mgaitan/cads/outputs/screenshots/AA/bottom.png

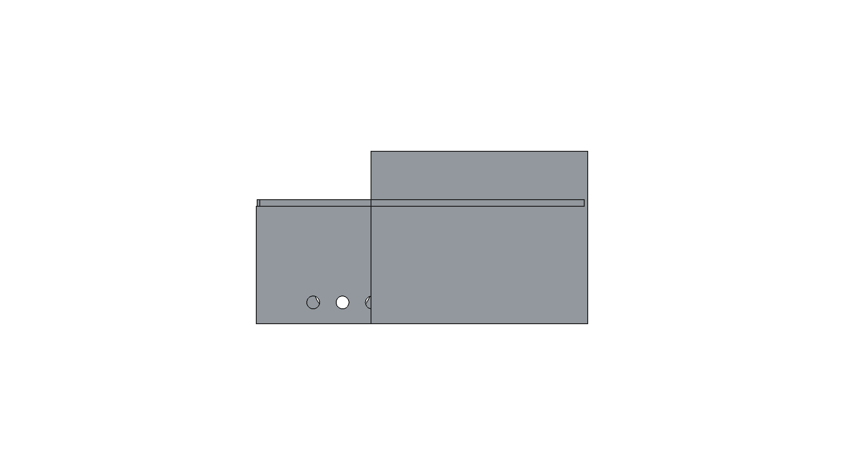
outputs/screenshots/AA/bottom.png
