mgaitan/cads/outputs/screenshots/AA/front.png

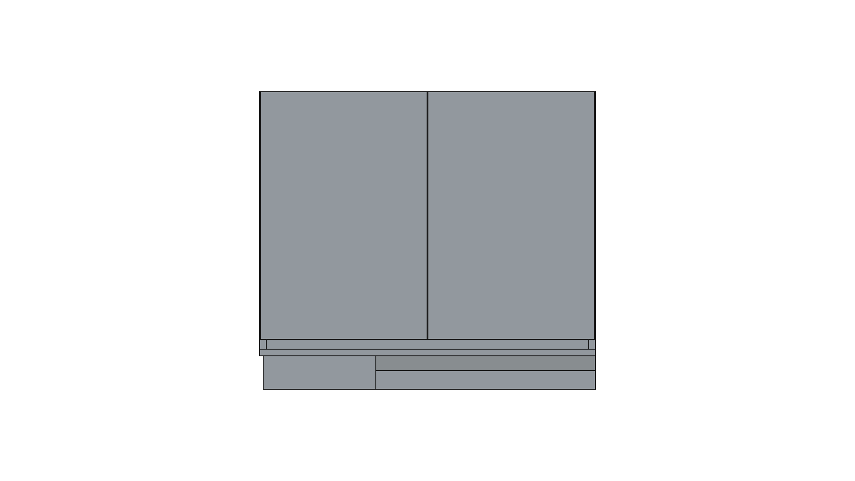
outputs/screenshots/AA/front.png
