mgaitan/cads/outputs/screenshots/AA/iso.png

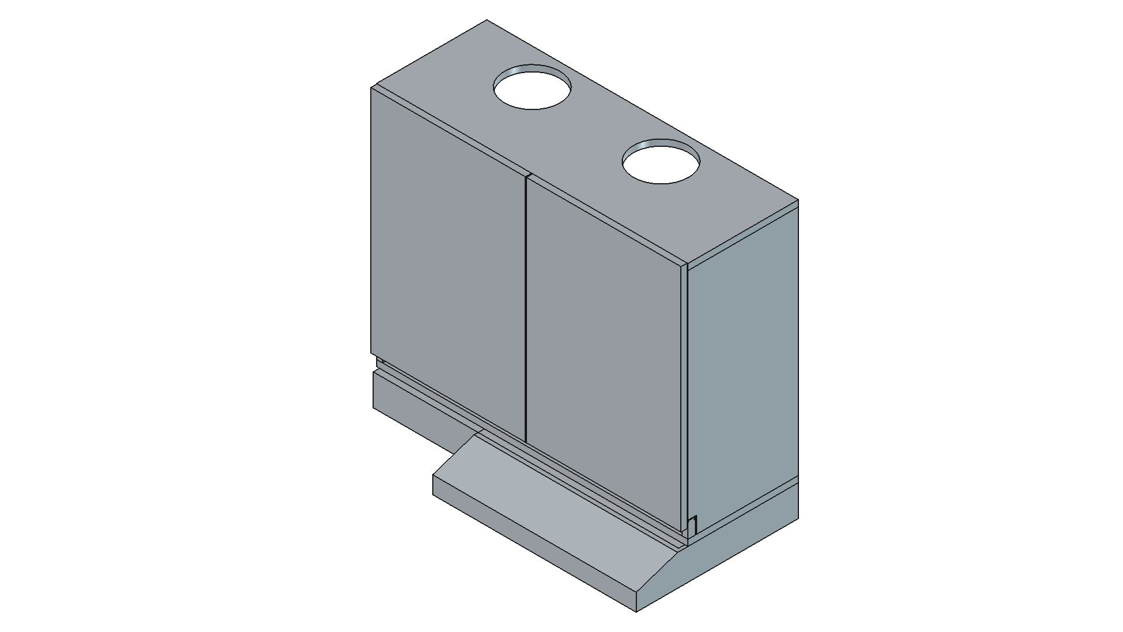
outputs/screenshots/AA/iso.png
