mgaitan/cads/outputs/screenshots/AA/left.png

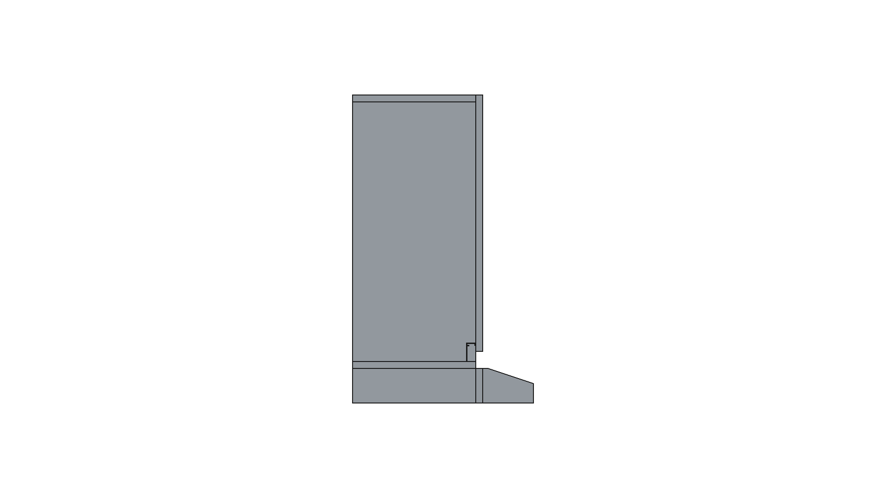
outputs/screenshots/AA/left.png
