mgaitan/cads/outputs/screenshots/AA/right.png

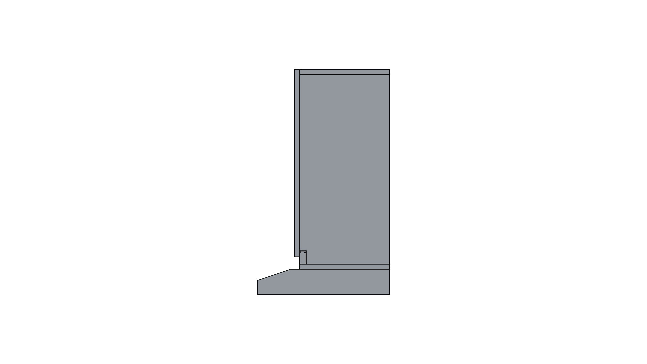
outputs/screenshots/AA/right.png
