mgaitan/cads/outputs/screenshots/AB/bottom.png

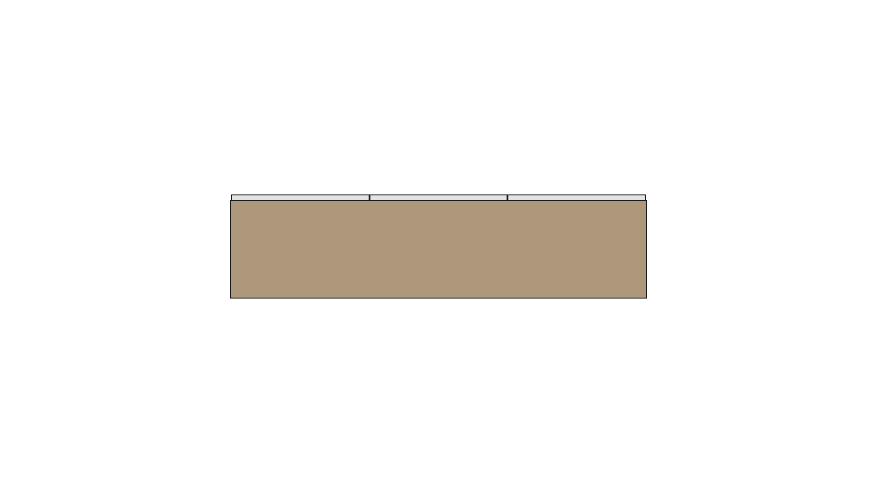
outputs/screenshots/AB/bottom.png
