mgaitan/cads/outputs/screenshots/AB/iso.png

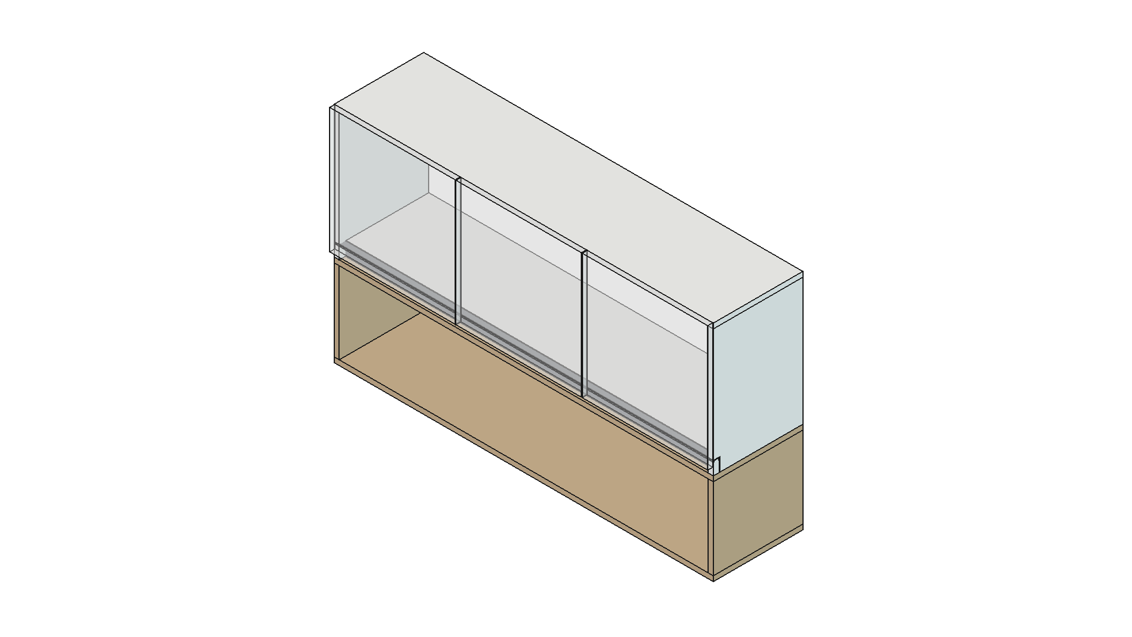
outputs/screenshots/AB/iso.png
