mgaitan/cads/outputs/screenshots/AB/left.png

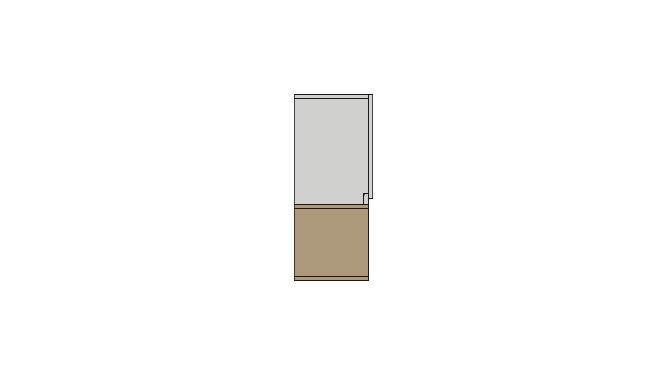
outputs/screenshots/AB/left.png
