mgaitan/cads/outputs/screenshots/BA/front.png

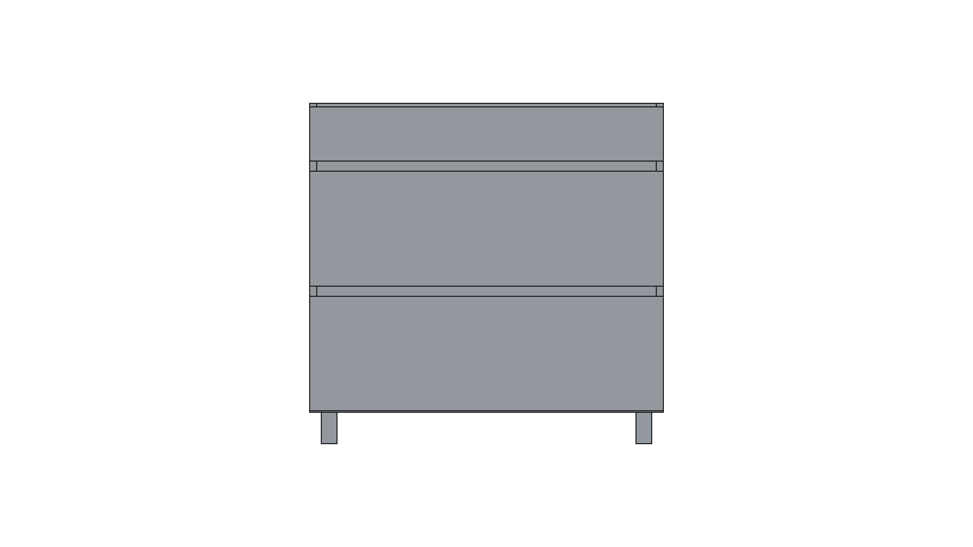
outputs/screenshots/BA/front.png
