mgaitan/cads/outputs/screenshots/BA/iso.png

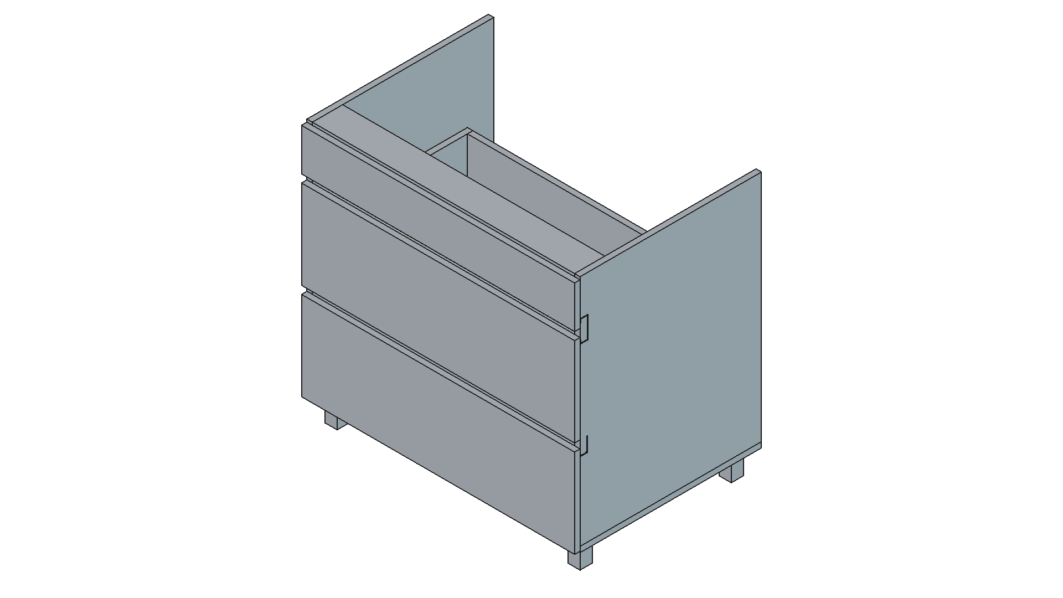
outputs/screenshots/BA/iso.png
