mgaitan/cads/outputs/screenshots/BB/top.png

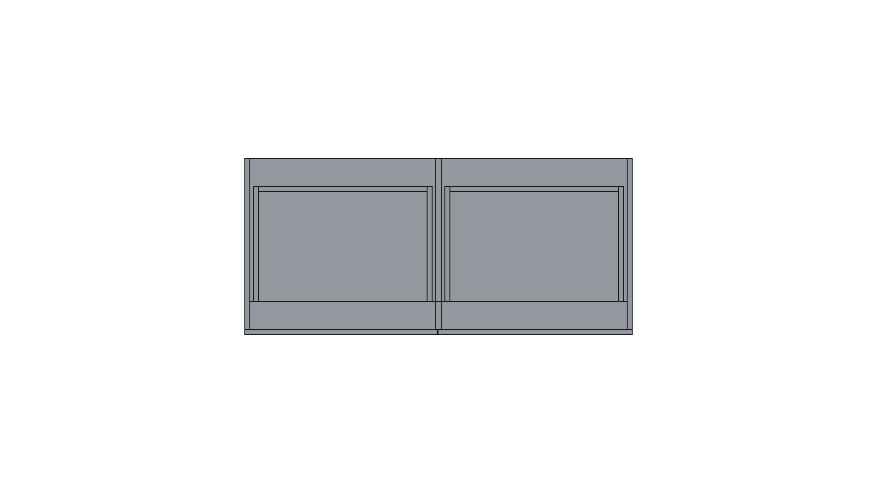
outputs/screenshots/BB/top.png
