mgaitan/cads/outputs/screenshots/ENS/bottom.png

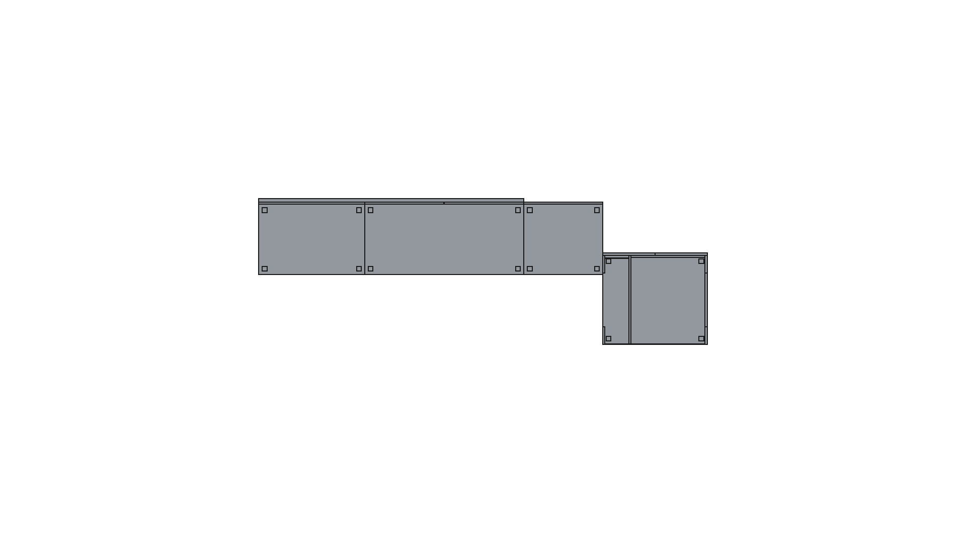
outputs/screenshots/ENS/bottom.png
