mgaitan/cads/outputs/screenshots/ENS/iso.png

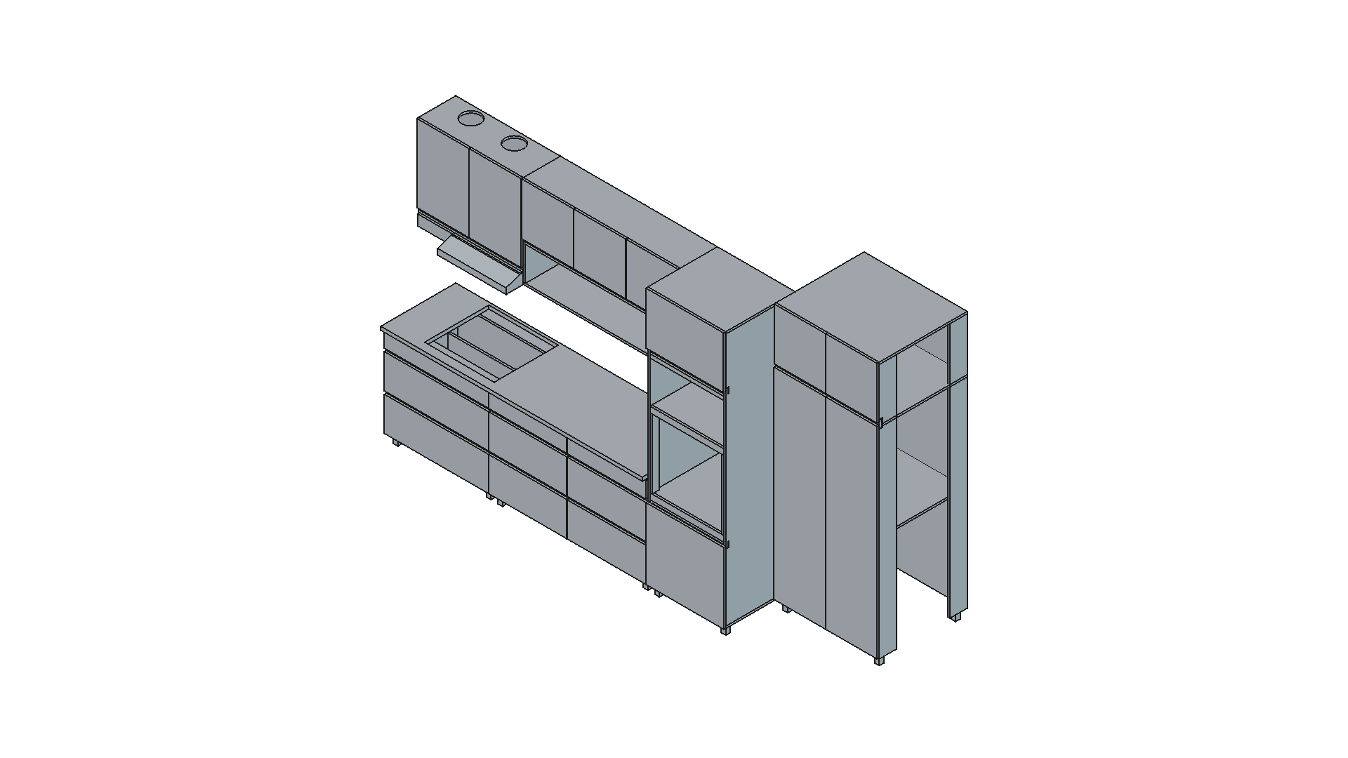
outputs/screenshots/ENS/iso.png
