mgaitan/cads/outputs/screenshots/ENS/top.png

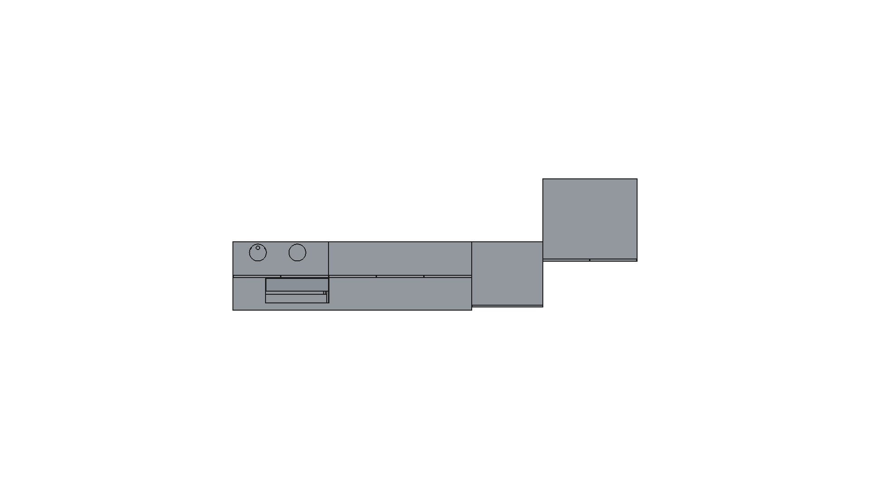
outputs/screenshots/ENS/top.png
