mgaitan/cads/outputs/screenshots/ENSI/front.png

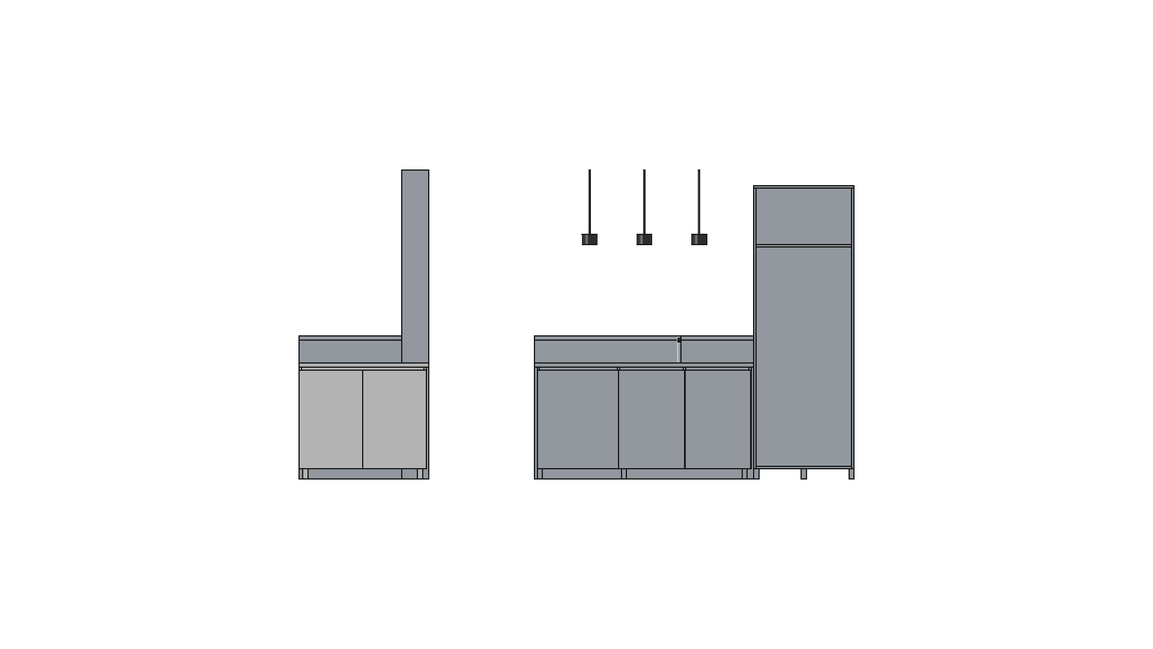
outputs/screenshots/ENSI/front.png
