mgaitan/cads/outputs/screenshots/ENSI/iso.png

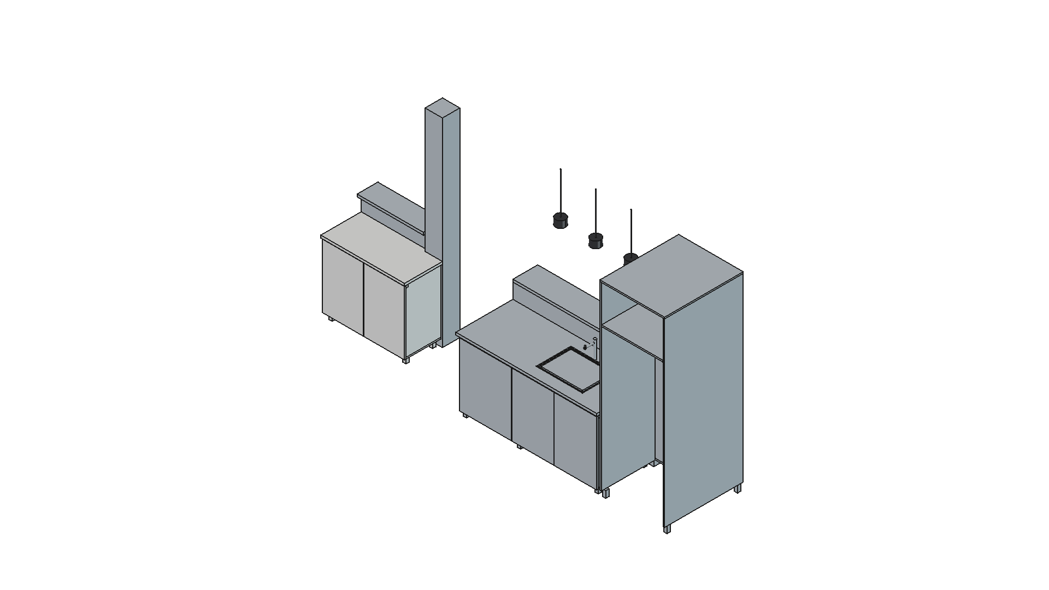
outputs/screenshots/ENSI/iso.png
