mgaitan/cads/outputs/screenshots/ENSI/rear.png

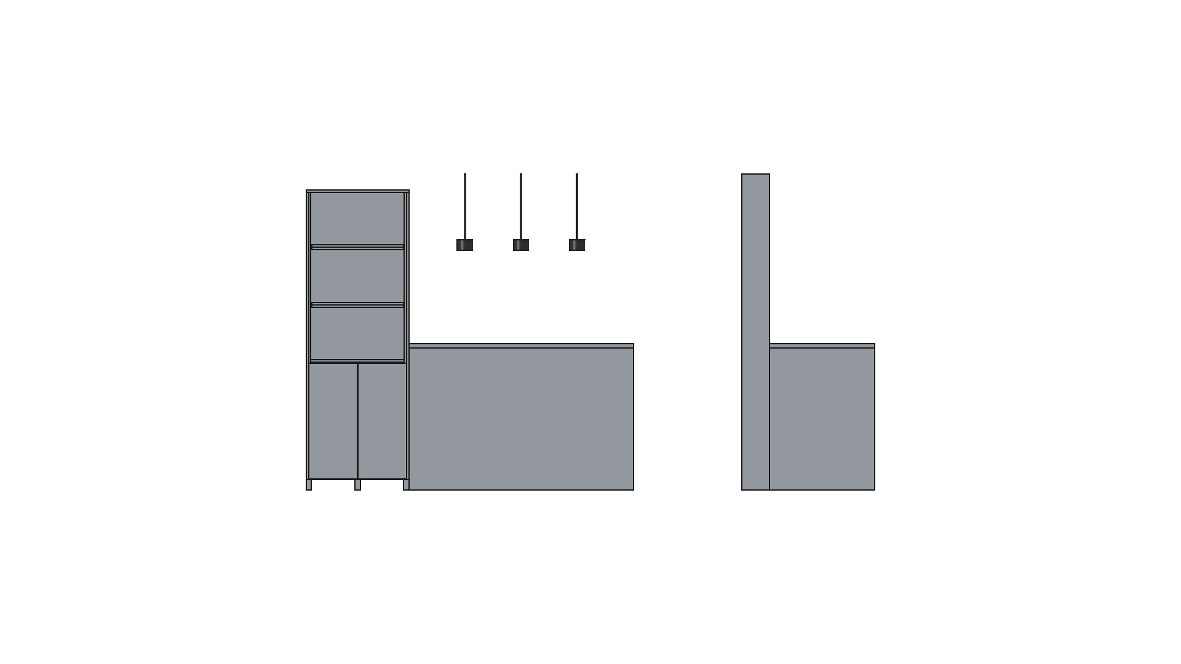
outputs/screenshots/ENSI/rear.png
