mgaitan/cads/outputs/screenshots/F/front.png

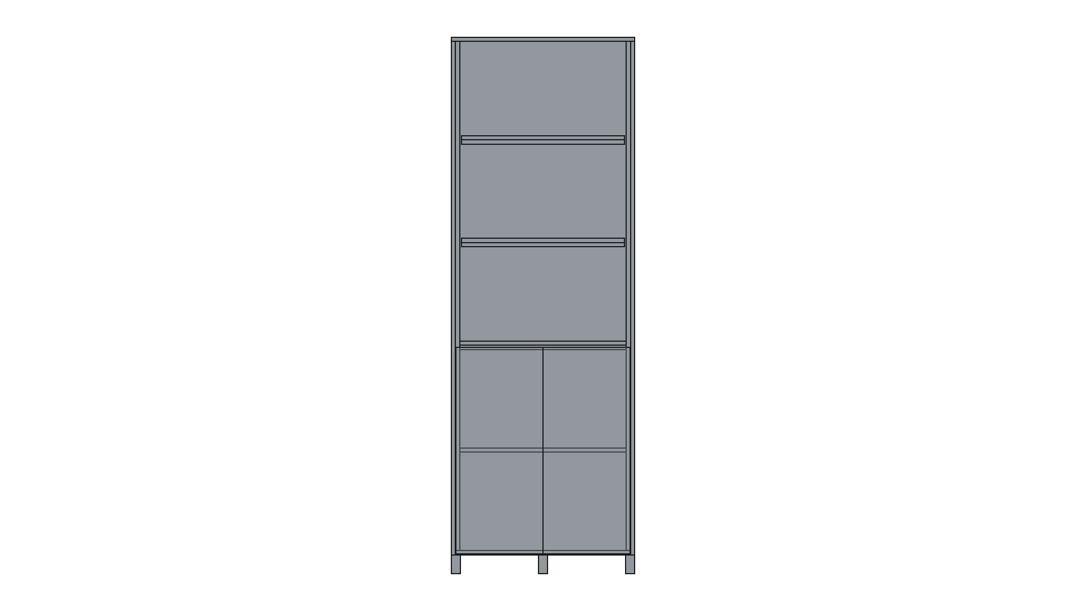
outputs/screenshots/F/front.png
