mgaitan/cads/outputs/screenshots/FULL/bottom.png

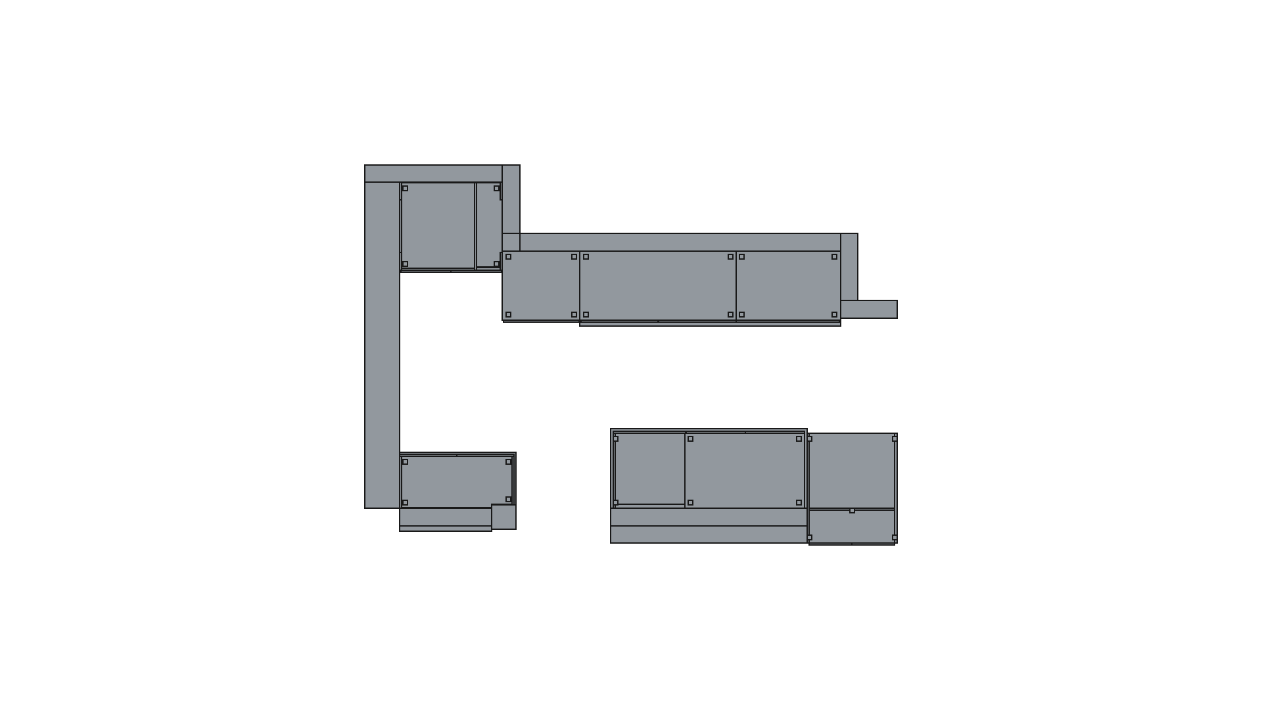
outputs/screenshots/FULL/bottom.png
