mgaitan/cads/outputs/screenshots/FULL/iso.png

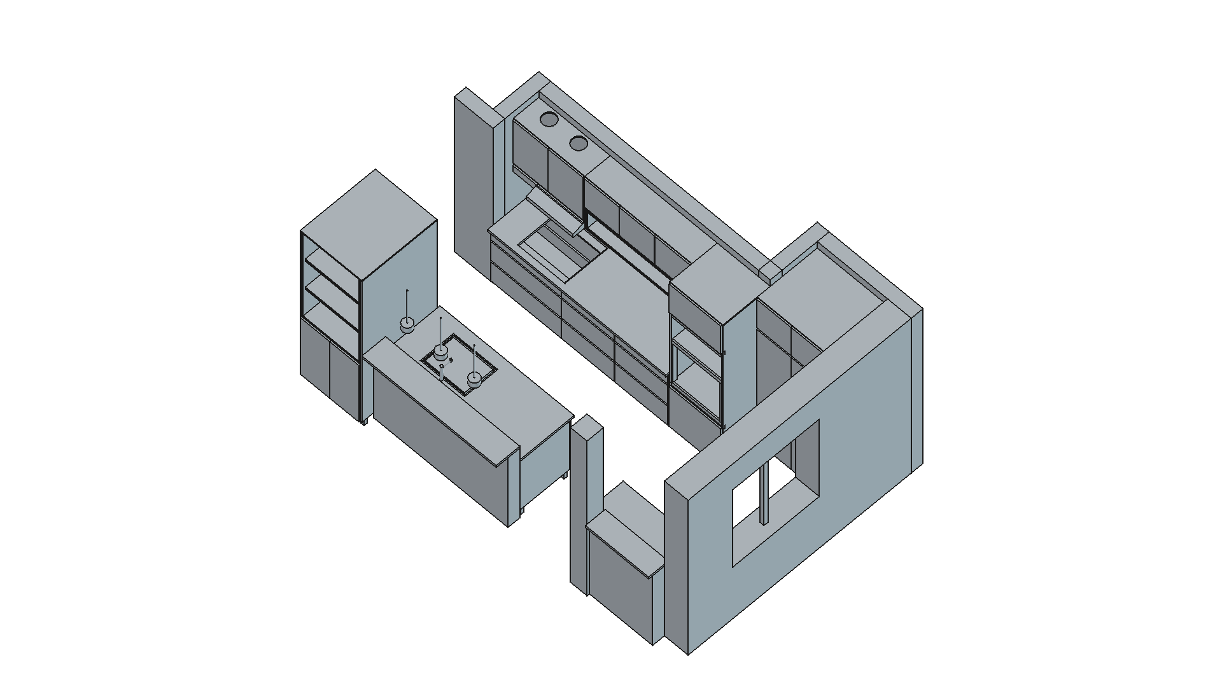
outputs/screenshots/FULL/iso.png
