mgaitan/cads/outputs/screenshots/FULL/left.png

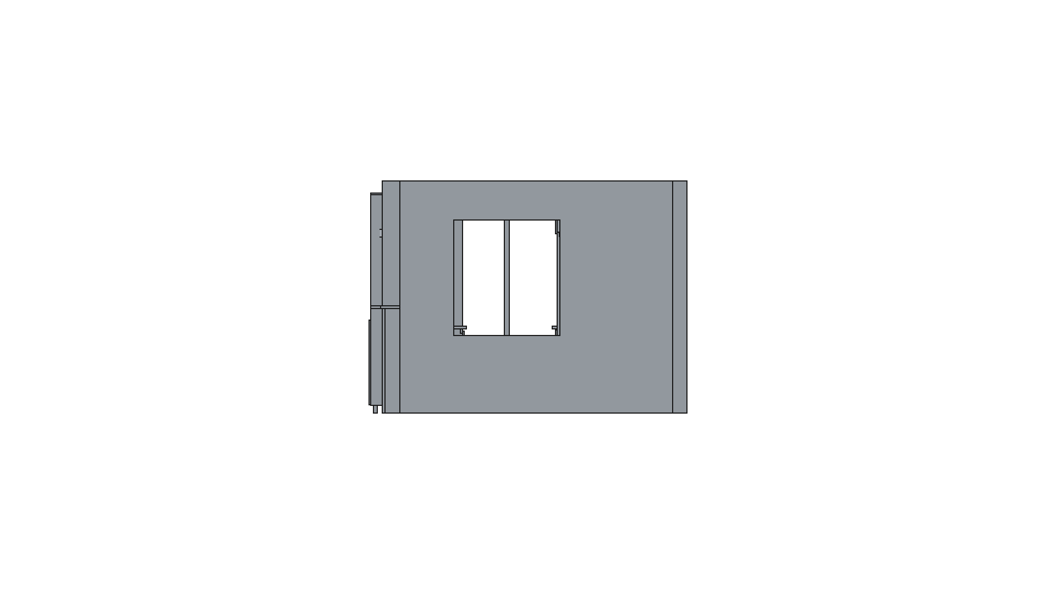
outputs/screenshots/FULL/left.png
