mgaitan/cads/outputs/screenshots/FULL/top.png

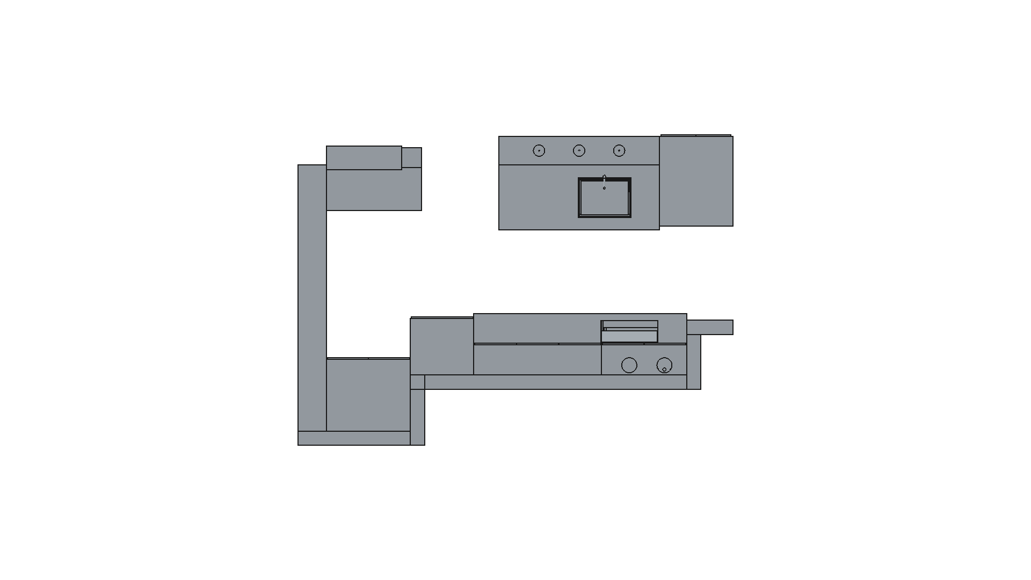
outputs/screenshots/FULL/top.png
