mgaitan/cads/outputs/screenshots/H/front.png

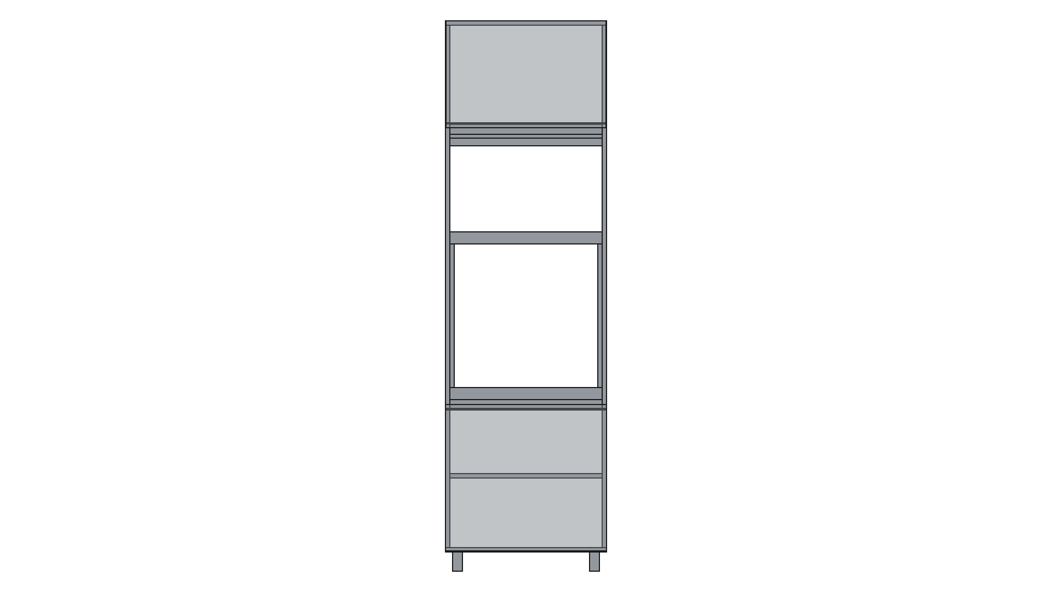
outputs/screenshots/H/front.png
