mgaitan/cads/outputs/screenshots/I/front.png

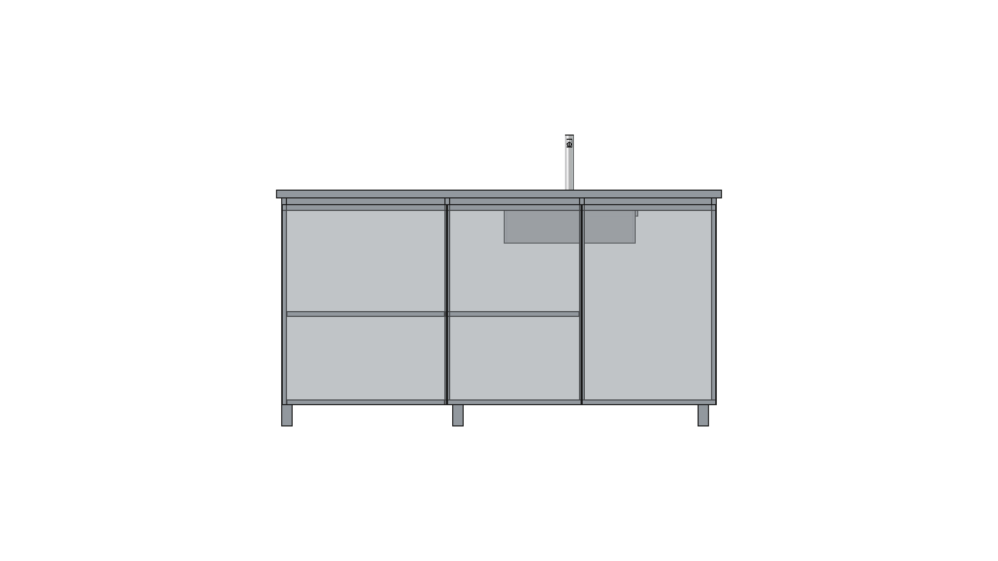
outputs/screenshots/I/front.png
