mgaitan/cads/outputs/screenshots/I/rear.png

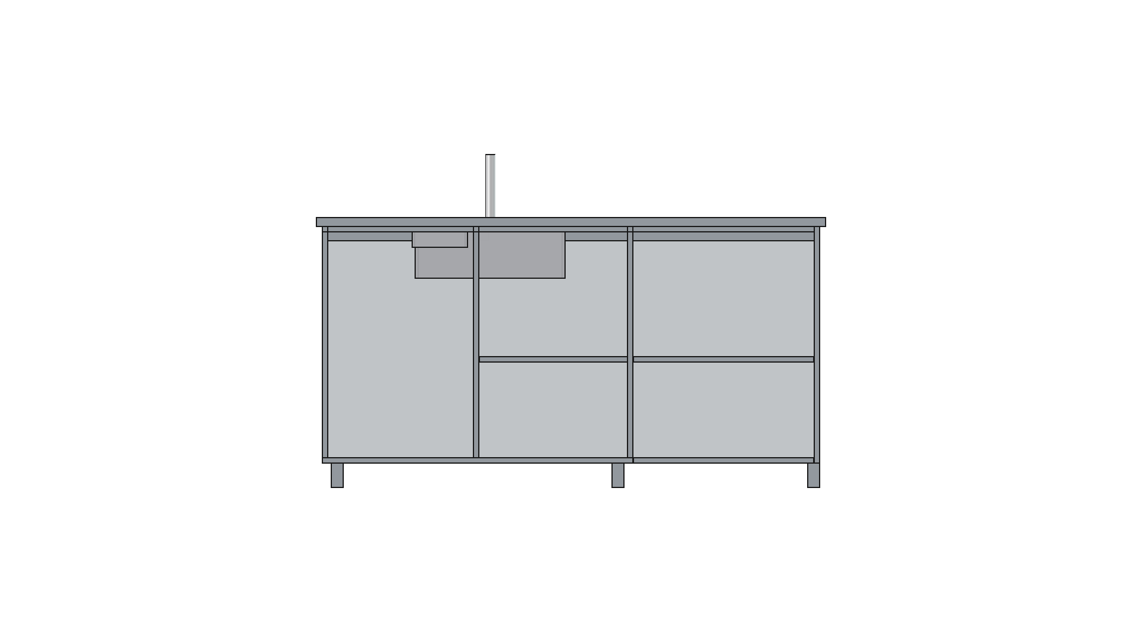
outputs/screenshots/I/rear.png
