mgaitan/cads/outputs/screenshots/M/bottom.png

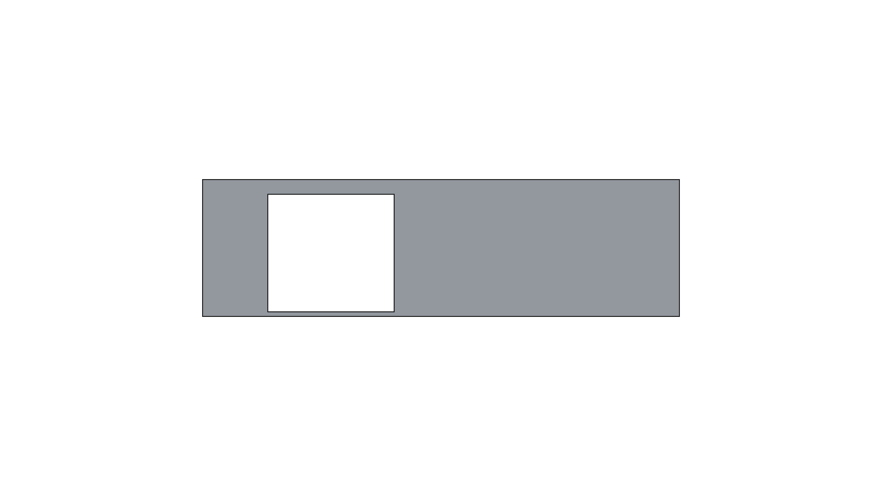
outputs/screenshots/M/bottom.png
