mgaitan/cads/outputs/screenshots/M/iso.png

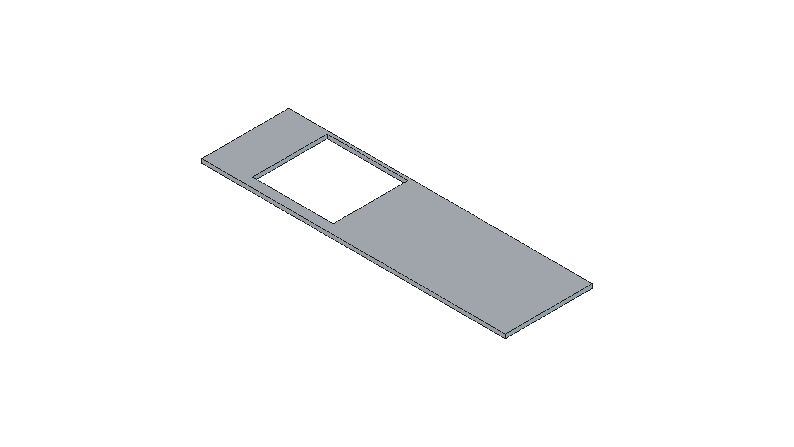
outputs/screenshots/M/iso.png
