mgaitan/cads/outputs/screenshots/R/rear.png

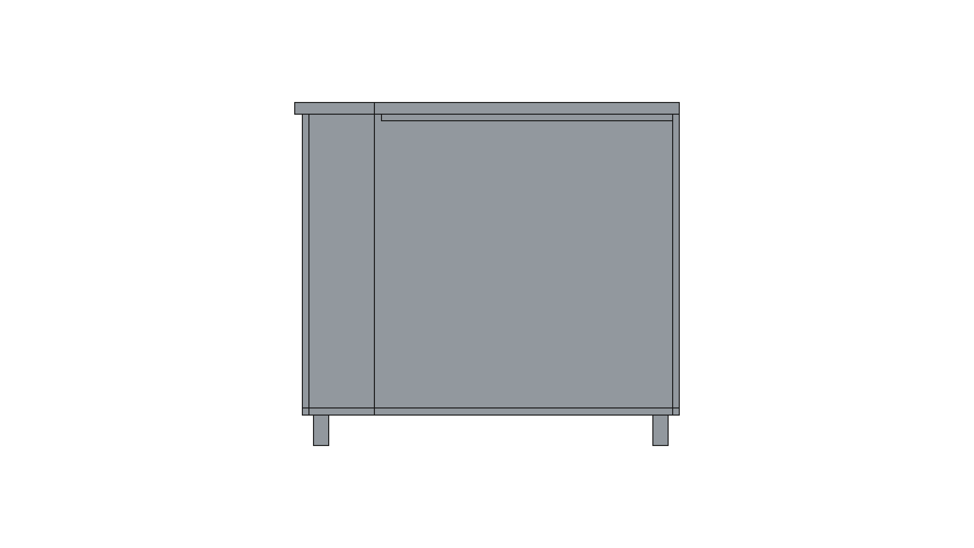
outputs/screenshots/R/rear.png
