mgaitan/cads/outputs/site/assets/models/AB.stl

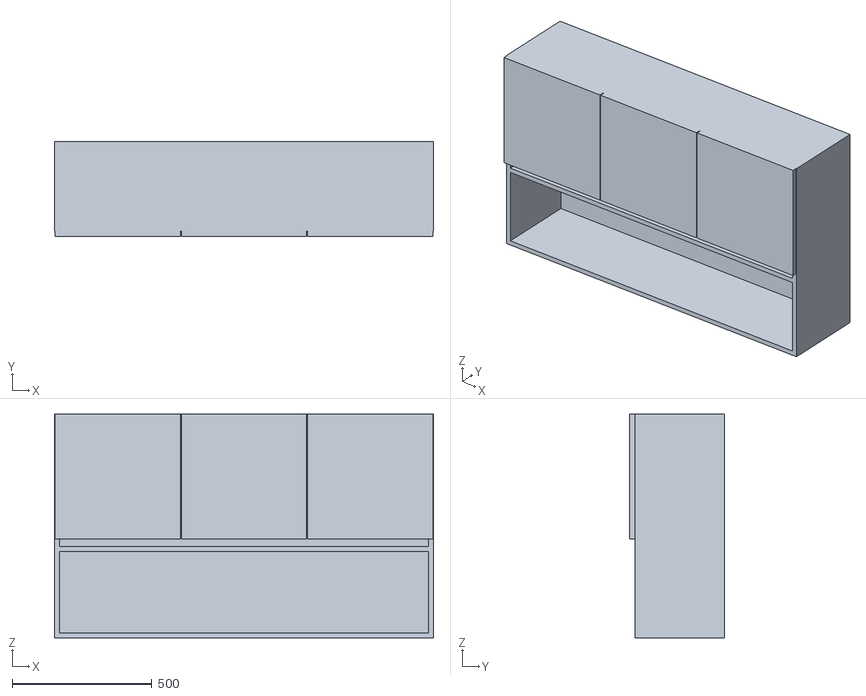
[picture p45: CAD file, 2026-03-17]
outputs/site/assets/models/AB.stl
1355.0 x 338.0 x 800.0
