mgaitan/cads/models/ENS.FCStd

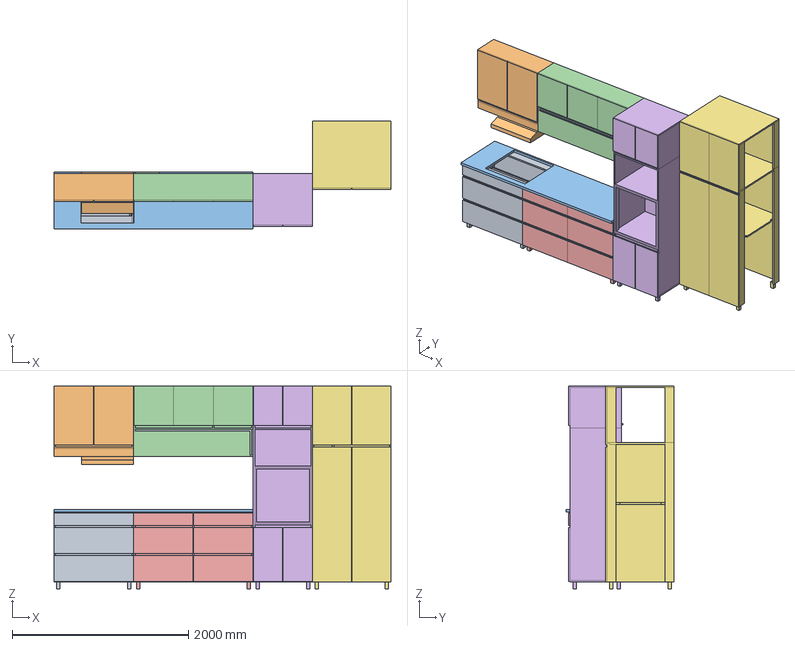
[picture p46: CAD file, 2026-03-25]
models/ENS.FCStd
3820.0 x 1225.0 x 2300.0 mm
BA_Bajo_Izq
AA_Alacena_Izq
M_Mesada
ABAC_Alacena_Der
BB_Bajo_Der
H_Columna
L_Armario_Lavadero
