mgaitan/cads/outputs/site/assets/models/BA.stl

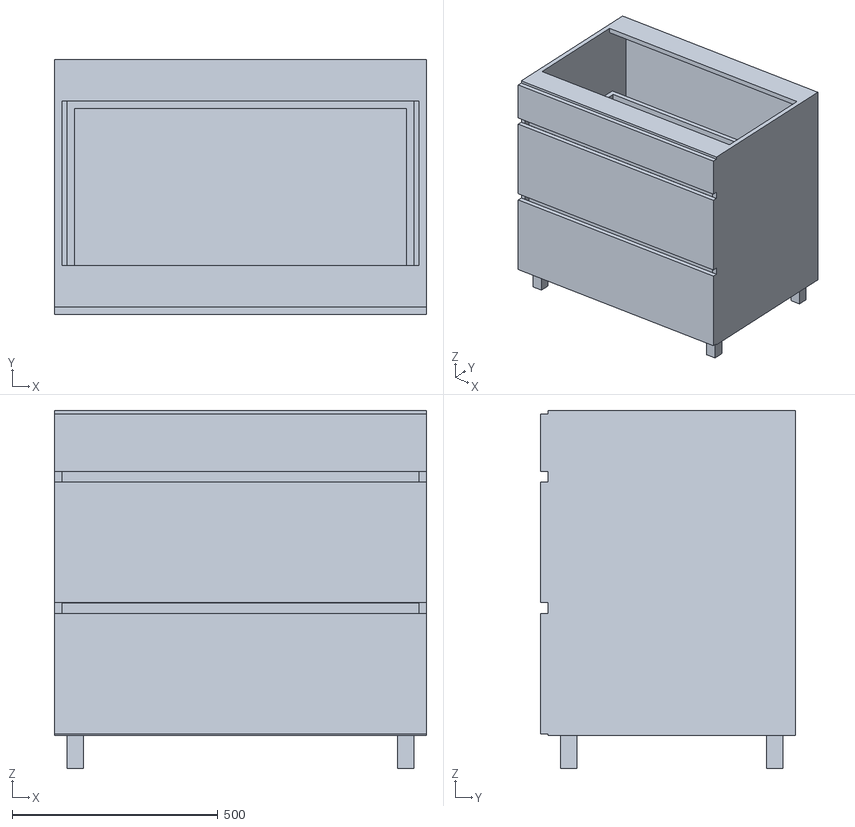
[picture p47: CAD file, 2026-03-17]
outputs/site/assets/models/BA.stl
903.0 x 618.0 x 870.0
