mgaitan/cads/models/AA.FCStd

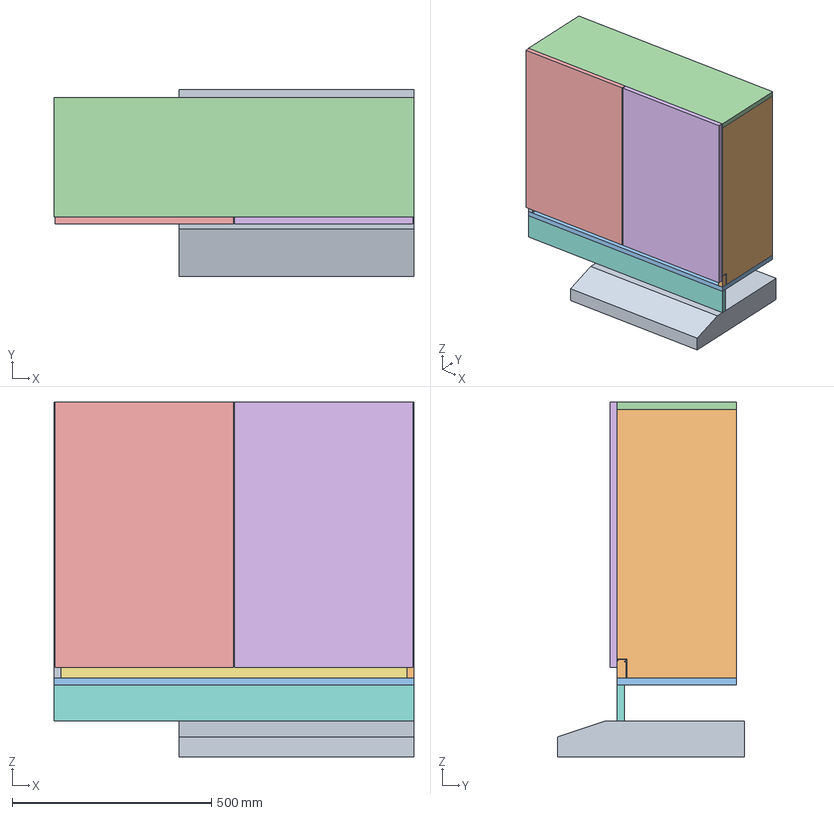
[picture p48: CAD file, 2026-03-25]
models/AA.FCStd
903.0 x 470.0 x 890.0 mm
AA1_Lateral_Izq
AA2_Lateral_Der
AA3_Piso_Casco
AA4_Tapa_Casco
AA8_Frente_Izq
AA9_Frente_Der
AA12_Gola_J_Inferior
AA10_Liston_Fijo_90
AA11_Extractor_Ref
