mgaitan/cads/outputs/site/assets/models/AA.stl

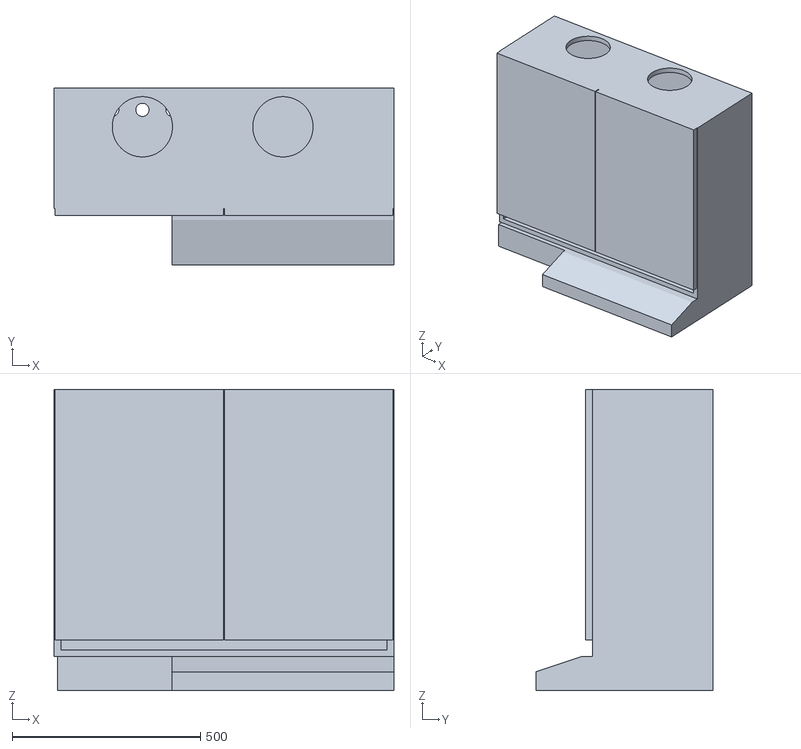
[picture p49: CAD file, 2026-03-17]
outputs/site/assets/models/AA.stl
903.0 x 470.0 x 800.0
