mgaitan/cads/models/H.FCStd

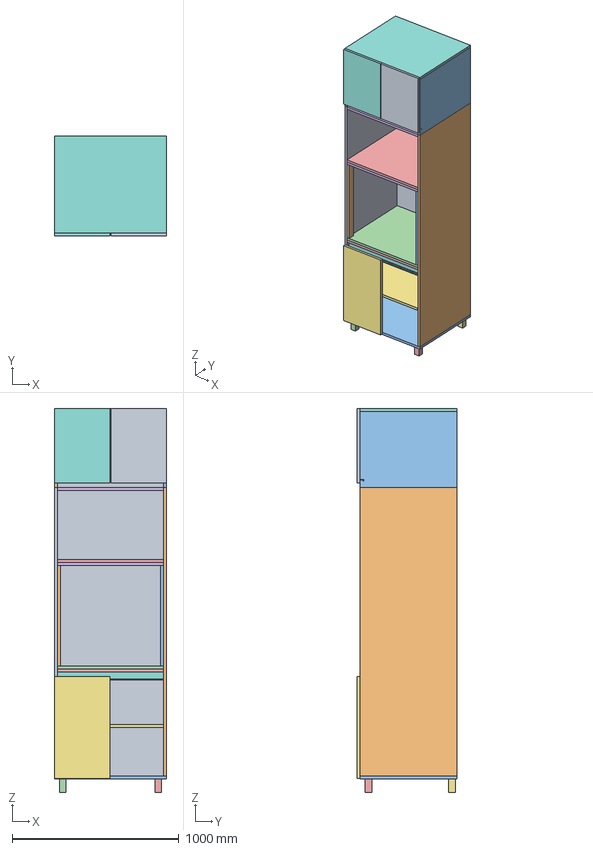
[picture p50: CAD file, 2026-03-19]
models/H.FCStd
672.0 x 598.0 x 2300.0 mm
H1_Lateral_Izq
H2_Lateral_Der
H3_Piso_Casco
H3L_Pata_1
H3L_Pata_2
H3L_Pata_3
H3L_Pata_4
H4_Tapa_Casco
H14_Fondo_3mm
H15_Liston_Vert_Izq
H16_Liston_Vert_Der
H5_Piso_Horno
H6_Piso_Micro
H7_Tapa_Micro
H8_Estante_Inferior
H17_Gola_J_Continuidad
H18_Gola_J_Sup
H1B_Lateral_Izq_Sup
H2B_Lateral_Der_Sup
H19_Piso_Alacena_Sup
H12B_Regrueso_Horizontal_Inferior_50
H9B_Regrueso_Horizontal_Sup_50
H10A_Puerta_Inferior_Izq
H11A_Puerta_Superior_Izq
H11B_Puerta_Superior_Der
