mgaitan/cads/outputs/site/assets/models/F.stl

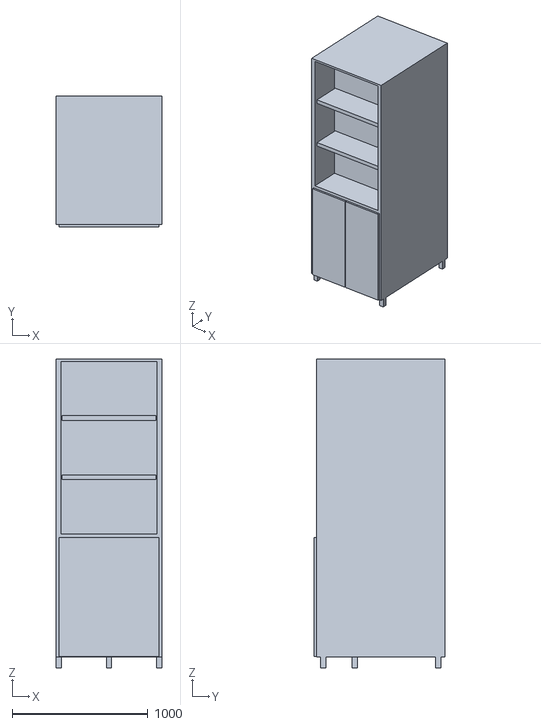
[picture p51: CAD file, 2026-03-17]
outputs/site/assets/models/F.stl
780.0 x 968.0 x 2278.0
