mgaitan/cads/models/BB.FCStd

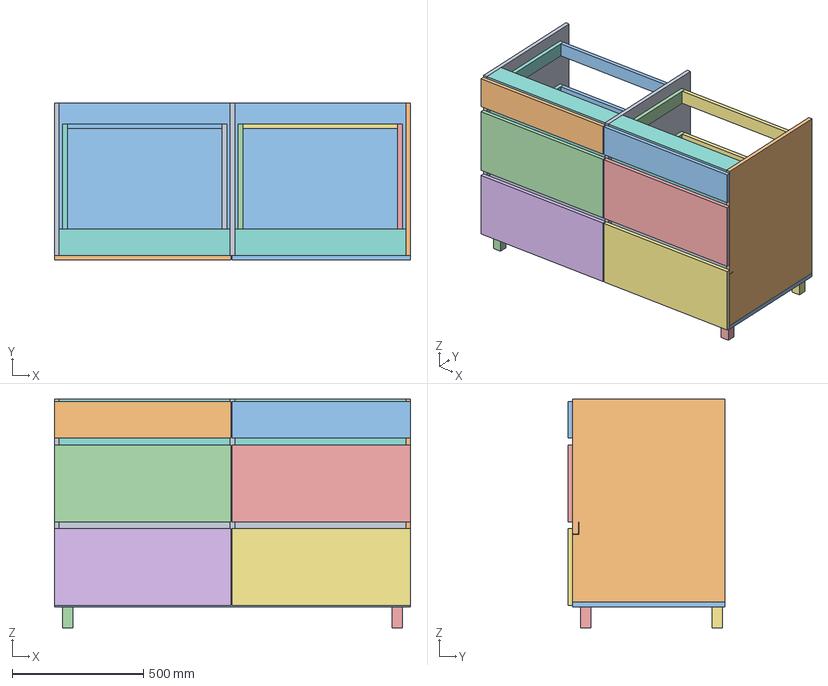
[picture p52: CAD file, 2026-03-19]
models/BB.FCStd
1355.0 x 598.0 x 870.0 mm
BB1_Lateral_Izq
BB2_Lateral_Der
BB3_Piso_Pasante
BB3L_Pata_1
BB3L_Pata_2
BB3L_Pata_3
BB3L_Pata_4
BB5_Soporte_Superior_Frente
BB7_Divisor_Central
BB8_Frente_Top_Izq
BB9_Frente_Top_Der
BB10_Frente_Mid_Izq
BB11_Frente_Mid_Der
BB12_Frente_Bot_Izq
BB13_Frente_Bot_Der
BB14_Caja_Top_Izq_Lateral_Izq
BB14_Caja_Top_Izq_Lateral_Der
BB14_Caja_Top_Izq_Frente_Caja
BB14_Caja_Top_Izq_Trasera_Caja
BB15_Caja_Top_Der_Lateral_Izq
BB15_Caja_Top_Der_Lateral_Der
BB15_Caja_Top_Der_Frente_Caja
BB15_Caja_Top_Der_Trasera_Caja
BB16_Caja_Mid_Izq_Lateral_Izq
BB16_Caja_Mid_Izq_Lateral_Der
BB16_Caja_Mid_Izq_Frente_Caja
BB16_Caja_Mid_Izq_Trasera_Caja
BB17_Caja_Mid_Der_Lateral_Izq
BB17_Caja_Mid_Der_Lateral_Der
BB17_Caja_Mid_Der_Frente_Caja
BB17_Caja_Mid_Der_Trasera_Caja
BB18_Caja_Bot_Izq_Lateral_Izq
BB18_Caja_Bot_Izq_Lateral_Der
BB18_Caja_Bot_Izq_Frente_Caja
BB18_Caja_Bot_Izq_Trasera_Caja
BB19_Caja_Bot_Der_Lateral_Izq
BB19_Caja_Bot_Der_Lateral_Der
BB19_Caja_Bot_Der_Frente_Caja
BB19_Caja_Bot_Der_Trasera_Caja
BB20_Gola_C_Superior
BB21_Gola_J_Media
