mgaitan/cads/outputs/site/assets/models/R.stl

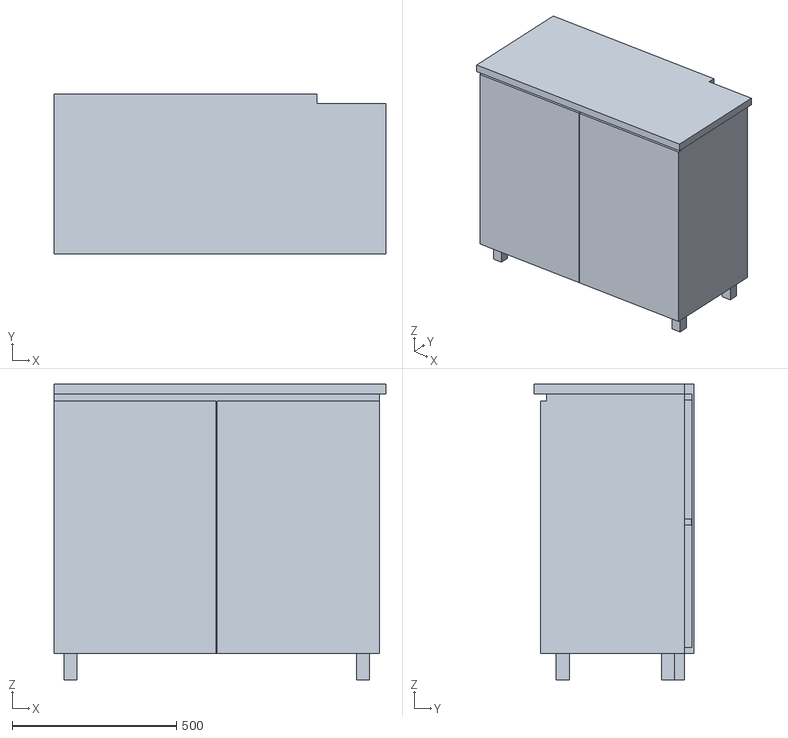
[picture p53: CAD file, 2026-03-17]
outputs/site/assets/models/R.stl
1010.0 x 488.0 x 900.0
