mgaitan/cads/models/AB.FCStd

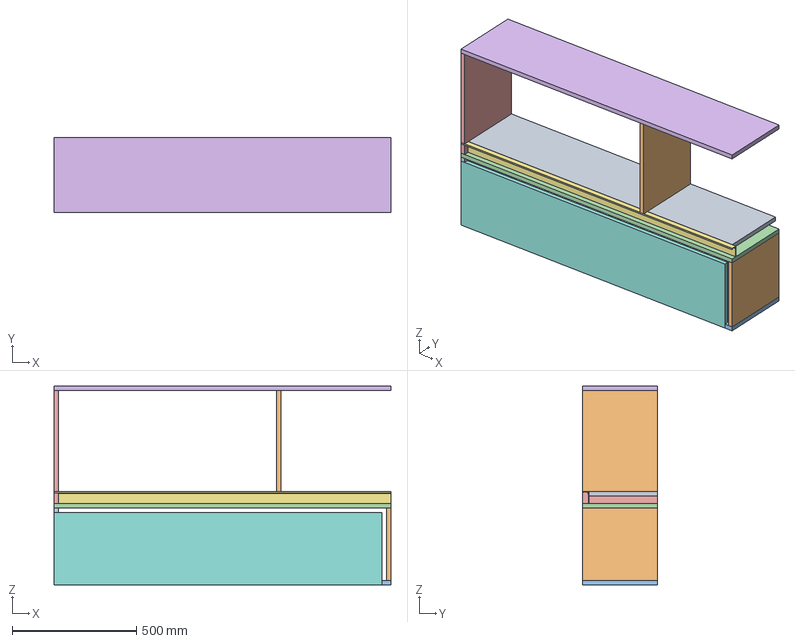
[picture p54: CAD file, 2026-03-19]
models/AB.FCStd
1355.0 x 300.0 x 800.0 mm
AC1_Lateral_Izq
AC2_Lateral_Der
AC3_Piso
AC4_Tapa
AB1_Lateral_Izq
AB4_Tapa
AB9_Gola_J_Inferior
AC5_Fondo_18mm
AB3_Piso
AB10_Divisor_Der_Puerta_Central
