mgaitan/cads/outputs/site/assets/models/BB.stl

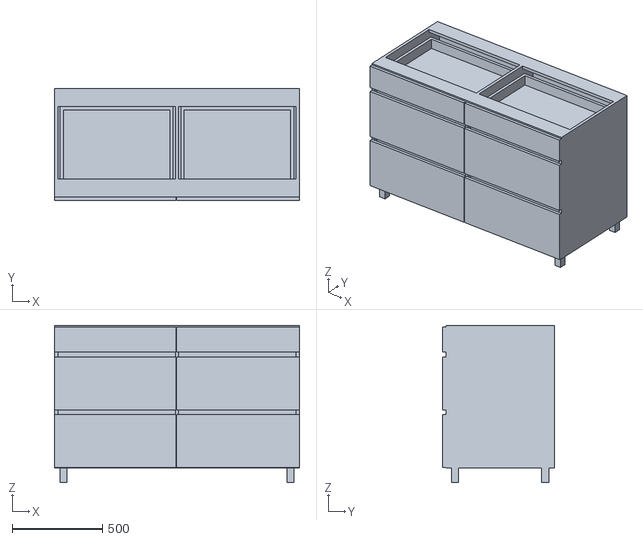
[picture p55: CAD file, 2026-03-17]
outputs/site/assets/models/BB.stl
1355.0 x 618.0 x 870.0
