mgaitan/cads/models/BA.FCStd

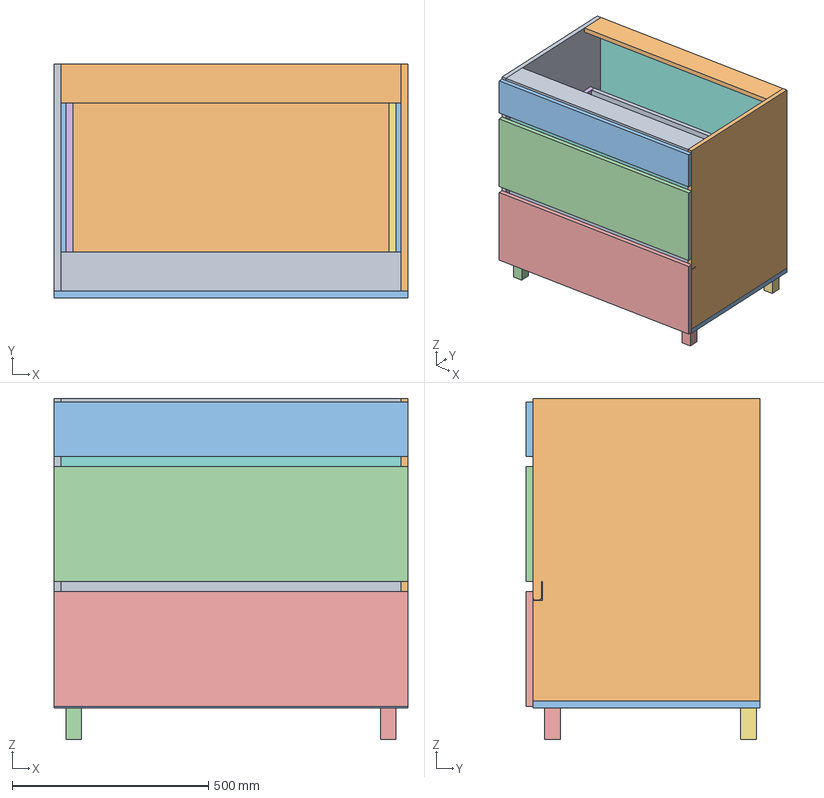
[picture p56: CAD file, 2026-03-19]
models/BA.FCStd
903.0 x 598.0 x 870.0 mm
BA1_Lateral_Izq
BA2_Lateral_Der
BA3_Piso_Pasante
BA3L_Pata_1
BA3L_Pata_2
BA3L_Pata_3
BA3L_Pata_4
BA4_Fondo_3mm
BA5_Soporte_Superior_Frente
BA6_Soporte_Superior_Fondo
BA9_Frente_Falso_Sup
BA10_Frente_Mid
BA11_Frente_Bot
BA14_Caja_Mid_Lateral_Izq
BA14_Caja_Mid_Lateral_Der
BA14_Caja_Mid_Frente_Caja
BA14_Caja_Mid_Trasera_Caja
BA14_Caja_Mid_Fondo_6mm
BA15_Caja_Bot_Lateral_Izq
BA15_Caja_Bot_Lateral_Der
BA15_Caja_Bot_Frente_Caja
BA15_Caja_Bot_Trasera_Caja
BA15_Caja_Bot_Fondo_6mm
BA12_Gola_C_Superior
BA13_Gola_J_Media
