mgaitan/cads/outputs/site/assets/models/M.stl

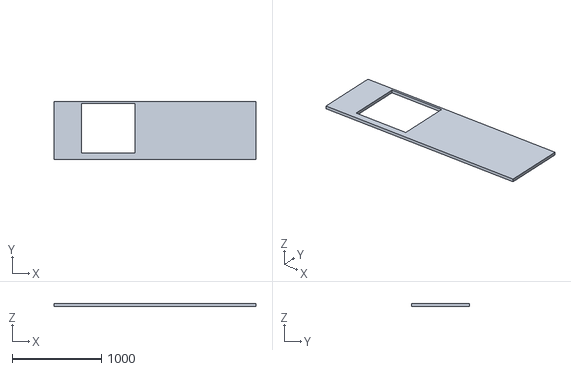
[picture p57: CAD file, 2026-03-12]
outputs/site/assets/models/M.stl
2258.0 x 648.0 x 30.0
