mgaitan/cads/models/R.FCStd

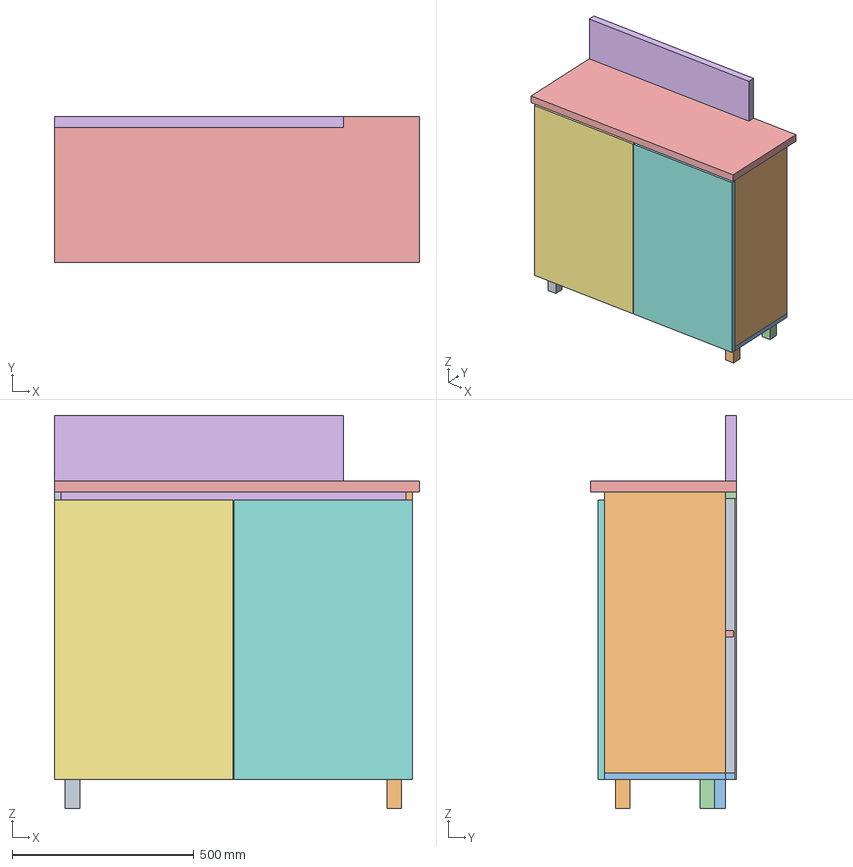
[picture p58: CAD file, 2026-03-19]
models/R.FCStd
1004.0 x 400.0 x 1080.0 mm
R1_Lateral_Izq
R2_Lateral_Der
R3_Piso
R5_Travesano_Sup_Trasero
R6_Estante_Regulable
R7_Gola_J_Superior
R8_Puerta_Izq
R9_Puerta_Der
R10_Pata_1
R10_Pata_2
R10_Pata_3
R10_Pata_4
R11_Mesada
R12_Alzada_Piedra
R4A_Fondo_3mm_Izq
R4B_Fondo_3mm_Der
