mgaitan/cads/models/L.FCStd

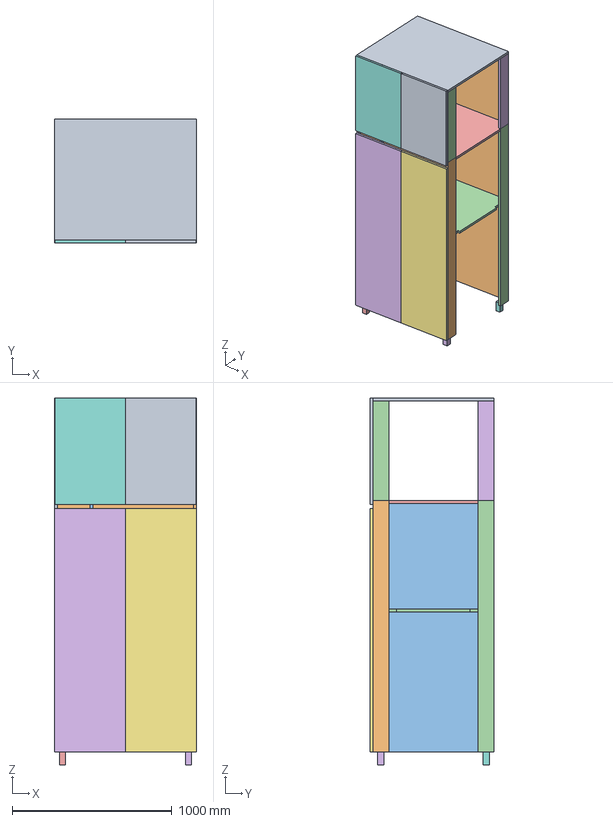
[picture p59: CAD file, 2026-03-18]
models/L.FCStd
890.0 x 778.0 x 2300.0 mm
L1_Parante_Front_Izq
L2_Parante_Front_Der
L15_Parante_Rear_Izq
L16_Parante_Rear_Der
L17_Pata_1
L17_Pata_2
L17_Pata_3
L17_Pata_4
L3_Tapa_Casco
L4_Fondo_3mm
L5_Parante_Interior
L6_Techo_Lavarropas_Der
L13_Piso_Modulo_Superior
L8_Puerta_Inf_Izq
L9_Puerta_Inf_Der
L10_Puerta_Sup_Izq
L11_Puerta_Sup_Der
L12_Gola_C_Media
L1B_Parante_Front_Izq_Sup
L2B_Parante_Front_Der_Sup
L15B_Parante_Rear_Izq_Sup
L16B_Parante_Rear_Der_Sup
